Thomas-Sparber/PiAMP/Drawings/Footswitch/Footswitch-1.3.png

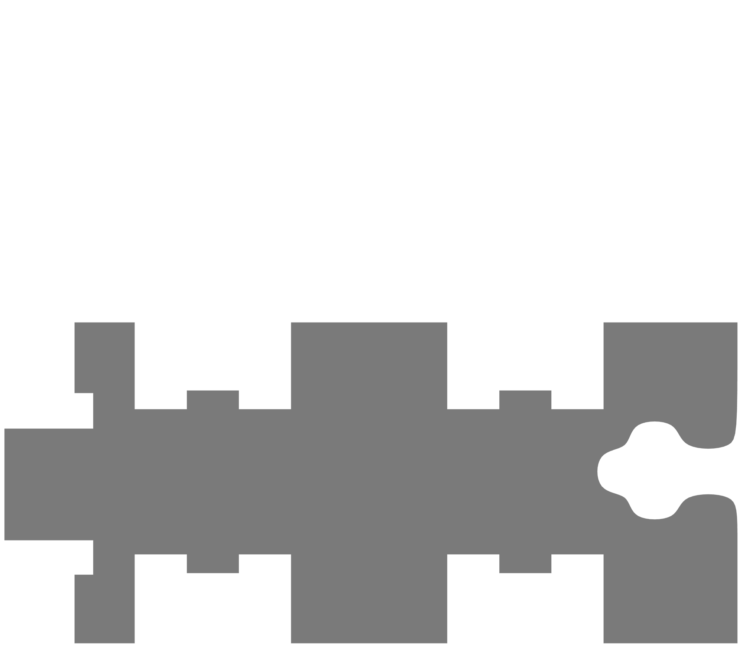
Drawings/Footswitch/Footswitch-1.3.png
