Thomas-Sparber/PiAMP/Drawings/Footswitch/Footswitch-1.4.png

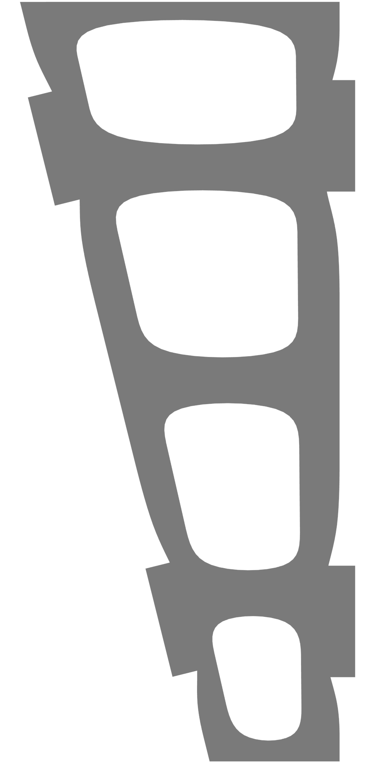
Drawings/Footswitch/Footswitch-1.4.png
