Thomas-Sparber/PiAMP/Drawings/Footswitch/Footswitch-2.0.png

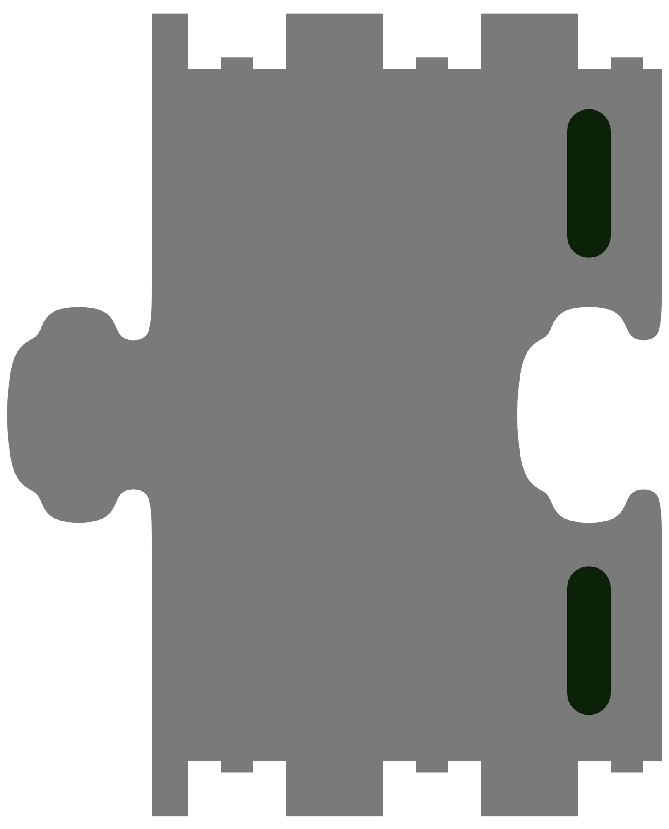
Drawings/Footswitch/Footswitch-2.0.png
