Thomas-Sparber/PiAMP/Drawings/Footswitch/Footswitch-2.1.png

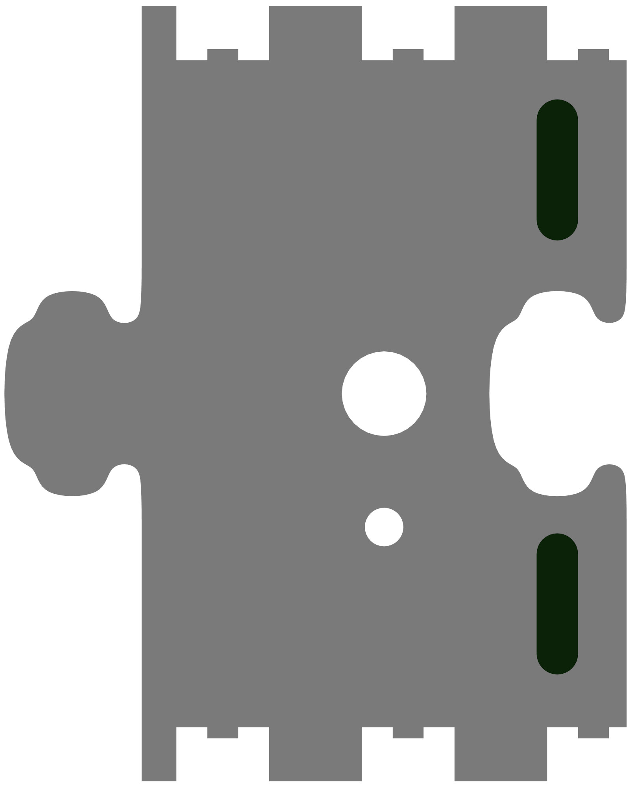
Drawings/Footswitch/Footswitch-2.1.png
