Thomas-Sparber/PiAMP/Drawings/Footswitch/Footswitch-2.2.png

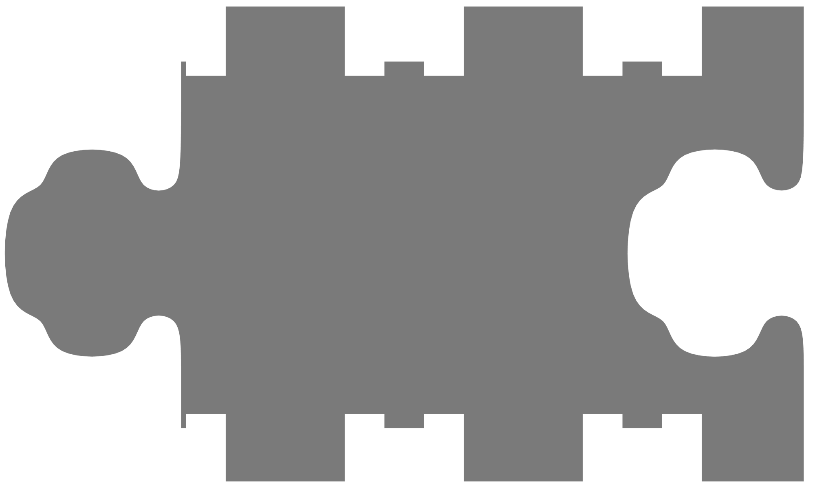
Drawings/Footswitch/Footswitch-2.2.png
