Thomas-Sparber/PiAMP/Drawings/Footswitch/Footswitch-2.3.png

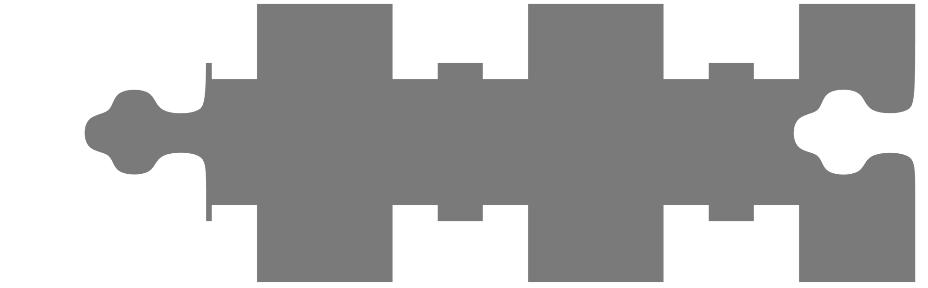
Drawings/Footswitch/Footswitch-2.3.png
