Thomas-Sparber/PiAMP/Drawings/Footswitch/Footswitch-3.1.png

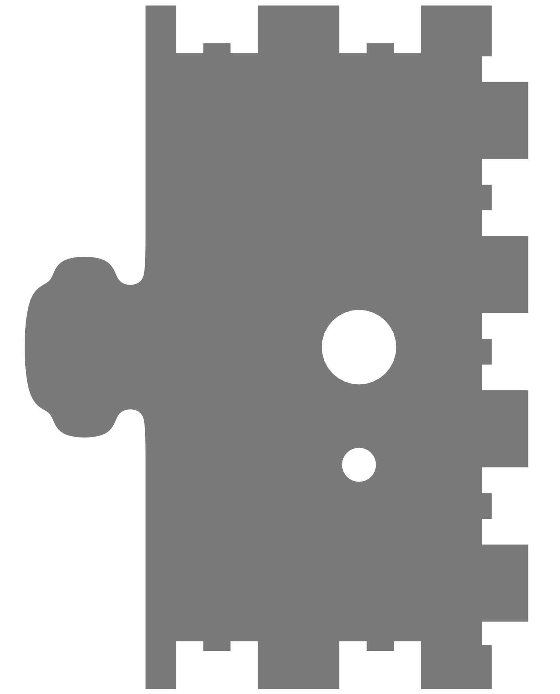
Drawings/Footswitch/Footswitch-3.1.png
