Thomas-Sparber/PiAMP/Drawings/Footswitch/Footswitch-3.2.png

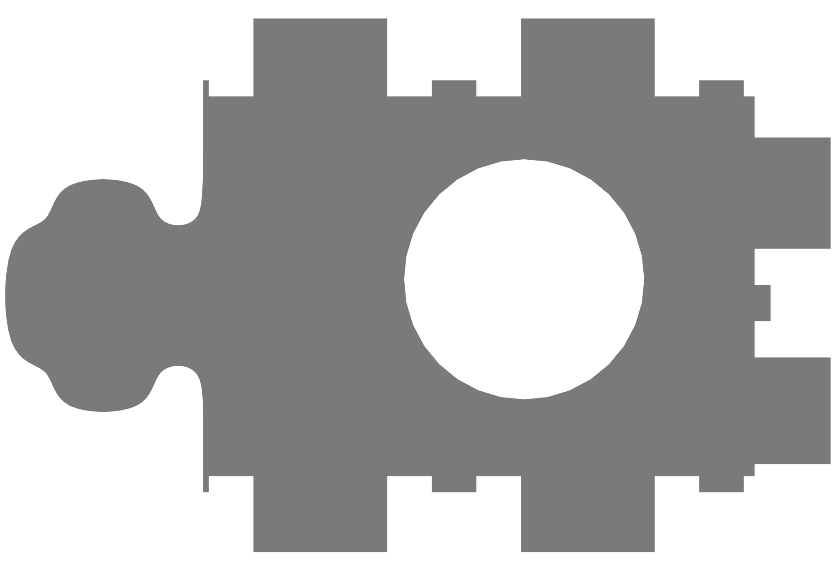
Drawings/Footswitch/Footswitch-3.2.png
