Thomas-Sparber/PiAMP/Drawings/Front-plate/Front-plate-no-knobs.png

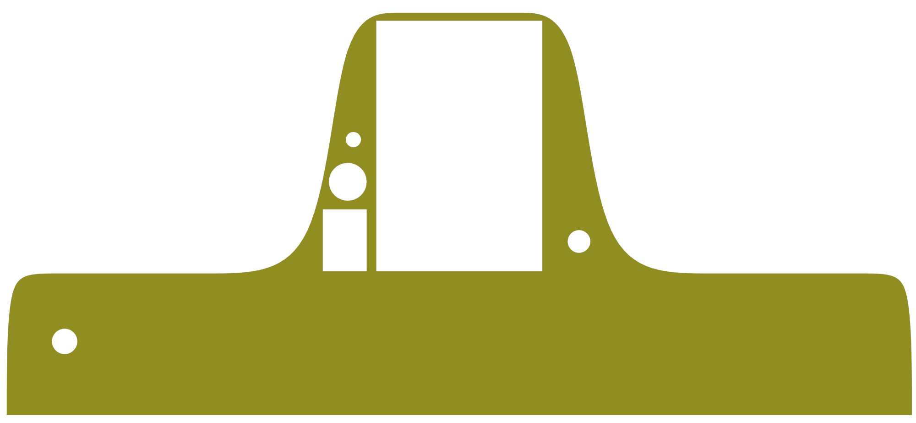
Drawings/Front-plate/Front-plate-no-knobs.png
