Thomas-Sparber/PiAMP/Controls/drawcommandtext.h

#pragma once

#include "drawcommand.h"

struct DrawCommandText : public DrawCommandHandler
{
  static DrawCommand* create(int16_t x, int16_t y, uint16_t w, uint16_t h, int16_t cursor_x, int16_t cursor_y, unsigned char r, unsigned char g, unsigned char b, const String &text, int16_t draw_x, int16_t draw_y, uint16_t draw_w, uint16_t draw_h)
  {
    DrawCommand *command = DrawCommand::create(DrawCommandType::Text, x, y, w, h, draw_x, draw_y, draw_w, draw_h);
    DrawCommandText *commandText = (DrawCommandText*)ReusableDrawCommands::get(DrawCommandType::Text);
    commandText->cursor_x = cursor_x;
    commandText->cursor_y = cursor_y;
    commandText->r = r;
    commandText->g = g;
    commandText->b = b;
    commandText->text = text;
    command->data = commandText;
    return command;
  }

  virtual void handle(LCDWIKI_KBV *mylcd, Font *font, int16_t /*x*/, int16_t /*y*/, uint16_t /*w*/, uint16_t /*h*/) override
  {
    unsigned int color = mylcd->Color_To_565(r, g, b);
    font->setTextColor(color);
    font->setCursor(cursor_x, cursor_y);
    font->print(text);
  }
  
  int16_t cursor_x;
  int16_t cursor_y;
  unsigned char r;
  unsigned char g;
  unsigned char b;
  String text;
};
